Jana-Marie/Enlightened-Otter/HW/V2.1/front.jpg

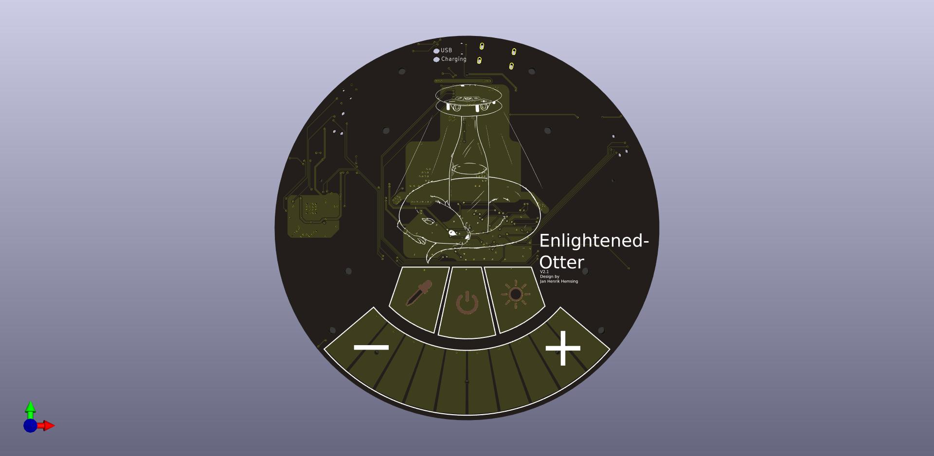
HW/V2.1/front.jpg
