Jana-Marie/Enlightened-Otter/Images/4cb7e35a-7c68-4c7e-90ba-2f1905d7ad42.jpeg

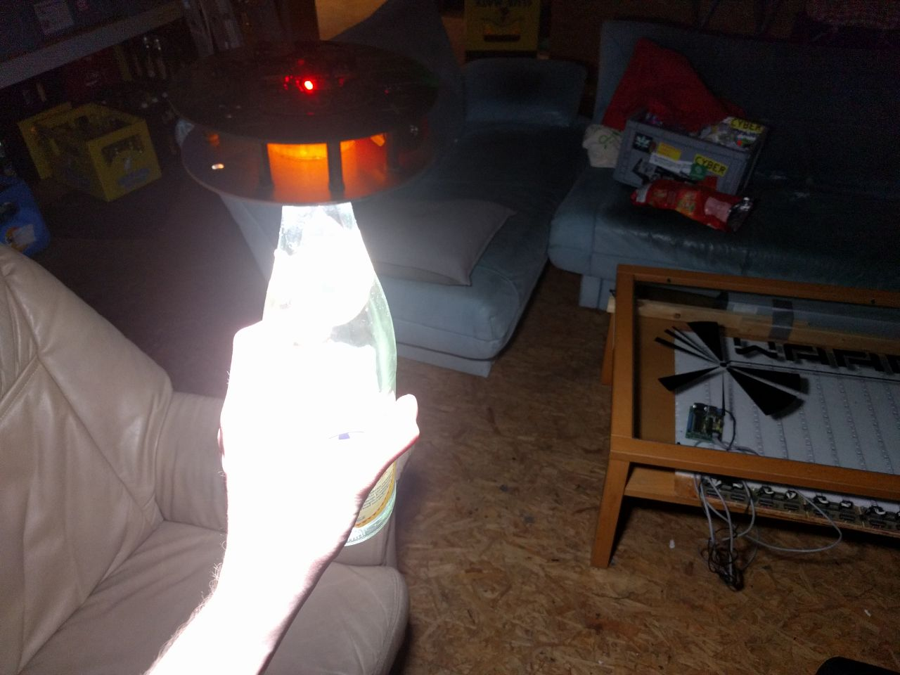
Images/4cb7e35a-7c68-4c7e-90ba-2f1905d7ad42.jpeg
