Jana-Marie/Enlightened-Otter/Images/final_kueche.jpeg

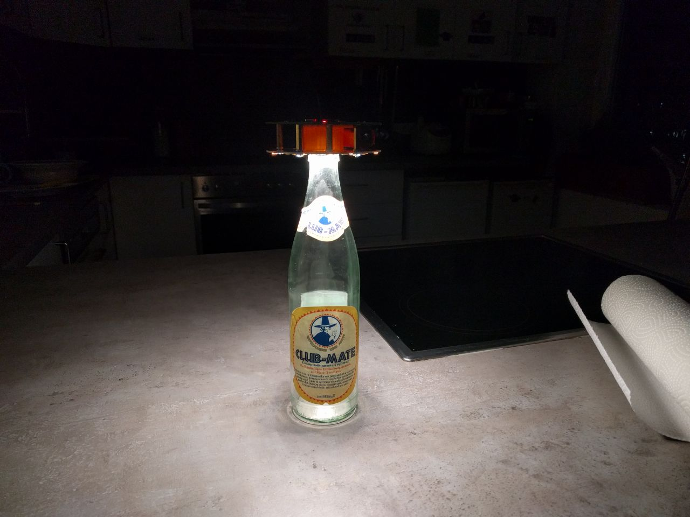
Images/final_kueche.jpeg
