Jana-Marie/Enlightened-Otter/Images/front_1.jpeg

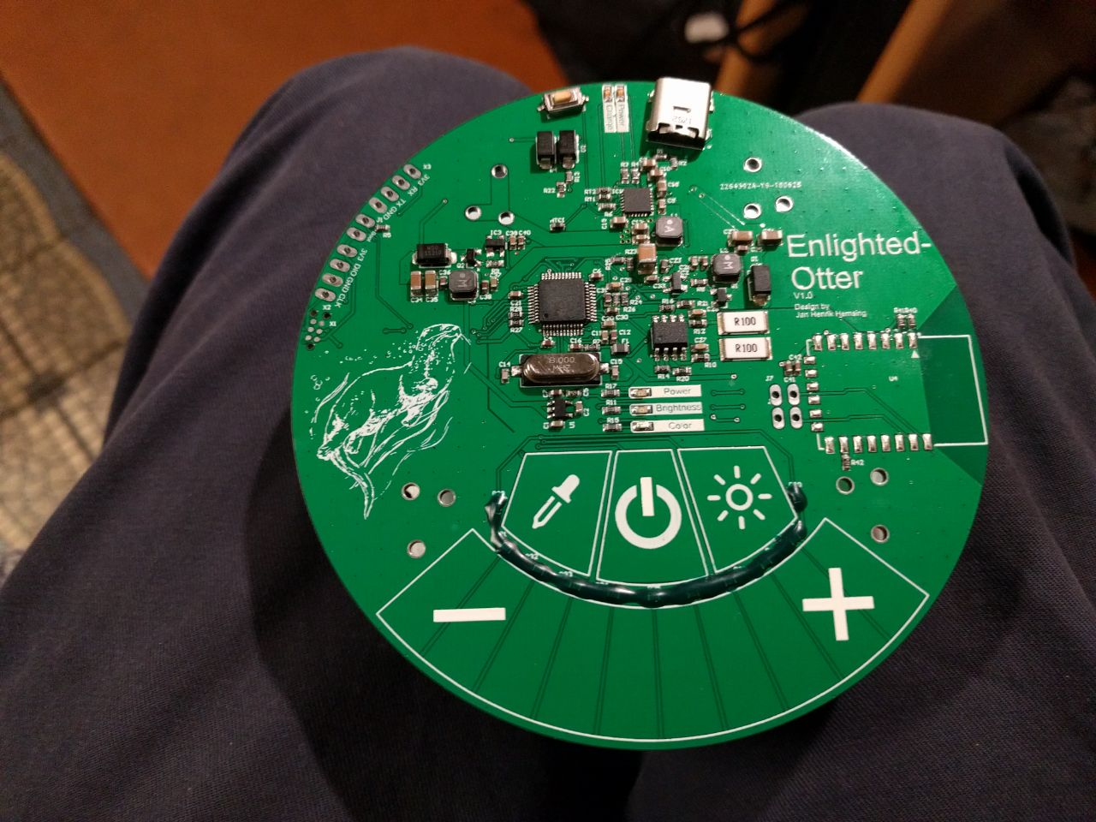
Images/front_1.jpeg
