Jana-Marie/Enlightened-Otter/Images/front_usb_1.jpeg

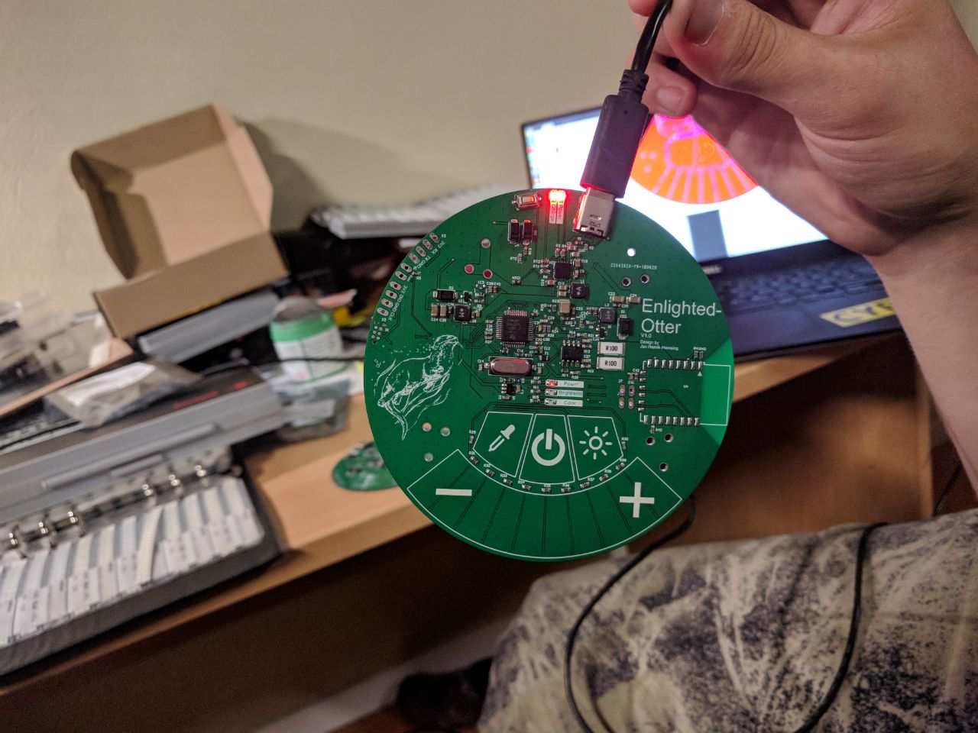
Images/front_usb_1.jpeg
