Jana-Marie/Enlightened-Otter/Images/light_1.jpeg

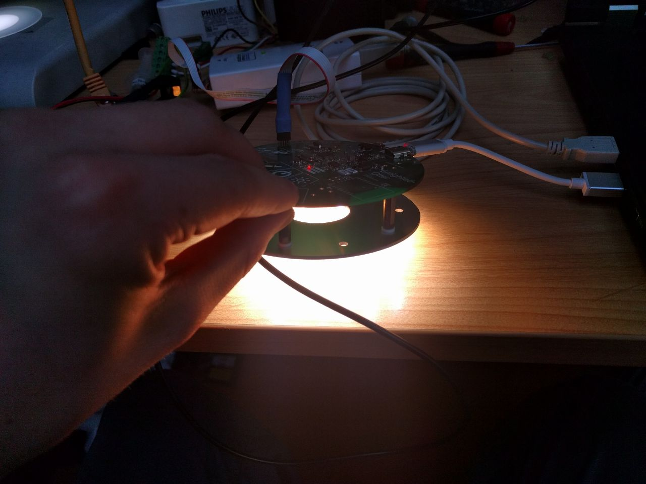
Images/light_1.jpeg
