Jana-Marie/Enlightened-Otter/Images/programming_1.jpeg

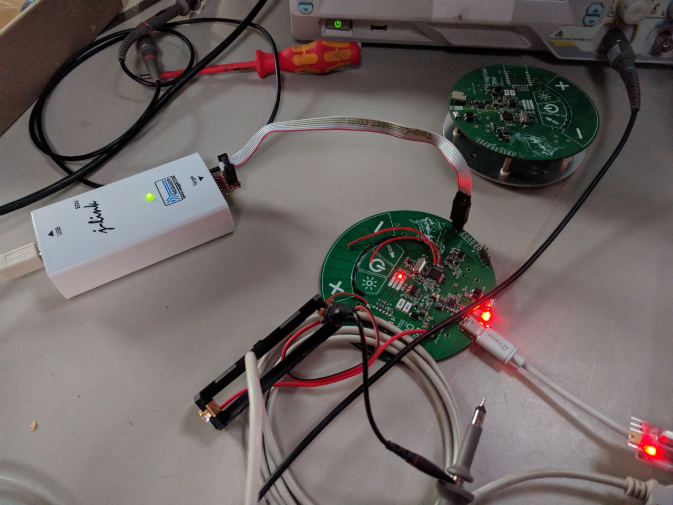
Images/programming_1.jpeg
