Jana-Marie/Enlightened-Otter/Images/spacer_3.jpeg

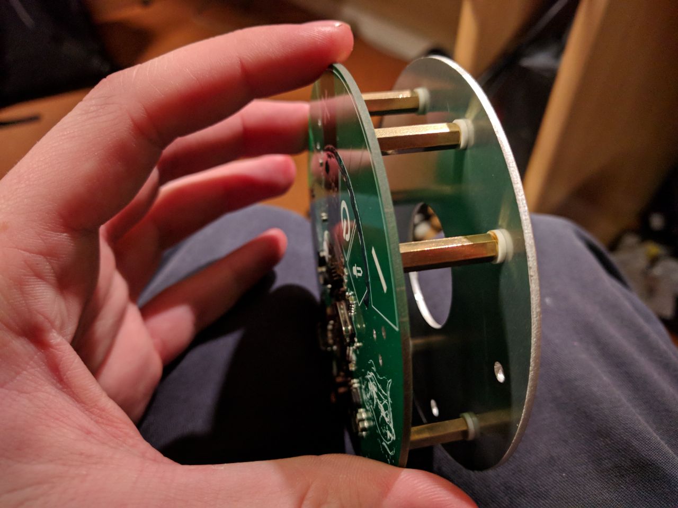
Images/spacer_3.jpeg
