Jana-Marie/Enlightened-Otter/Images/v21_1.jpg

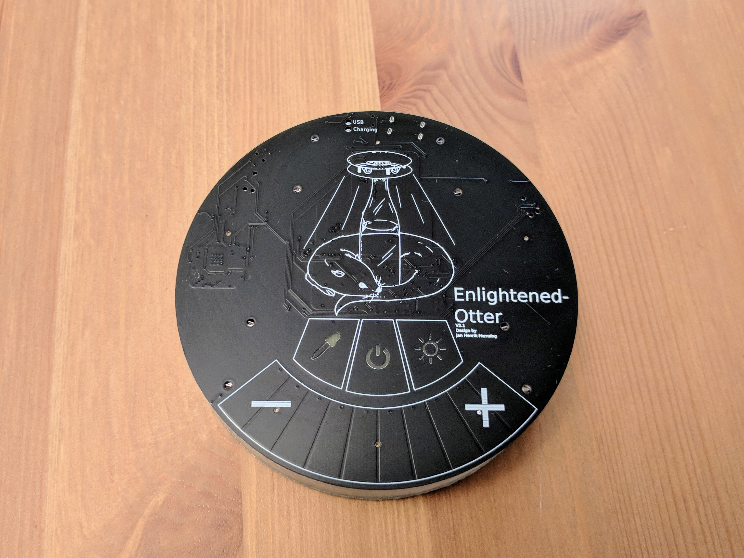
Images/v21_1.jpg
