Jana-Marie/Enlightened-Otter/Images/v21_back_2.jpg

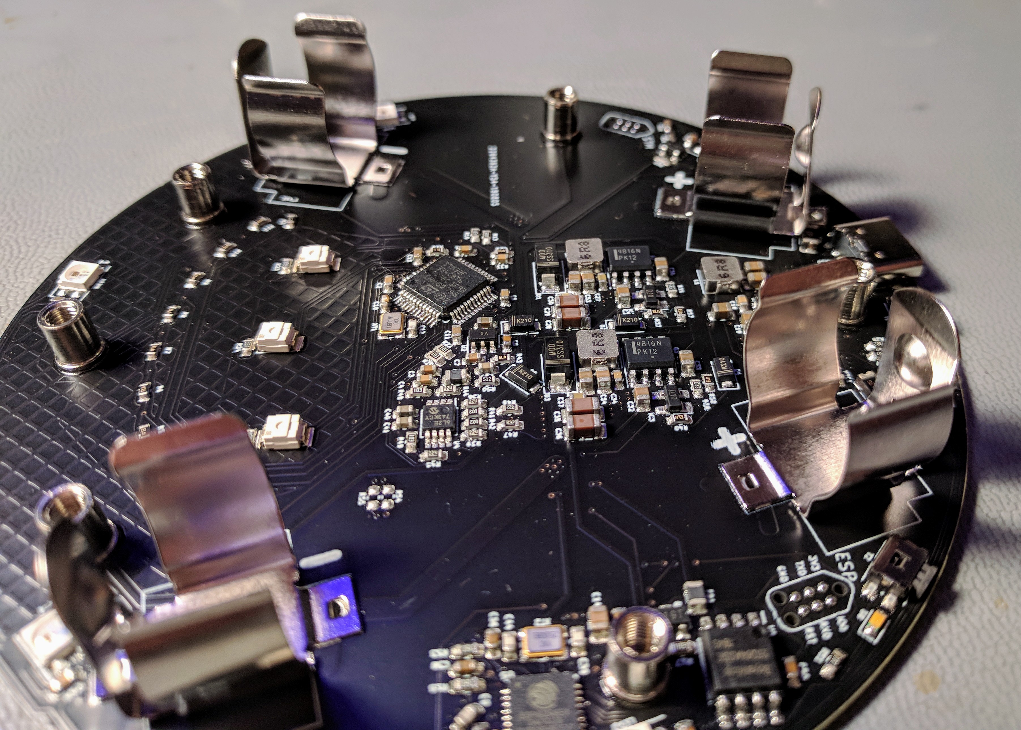
Images/v21_back_2.jpg
