Jana-Marie/Enlightened-Otter/Images/v21_mate_1.jpg

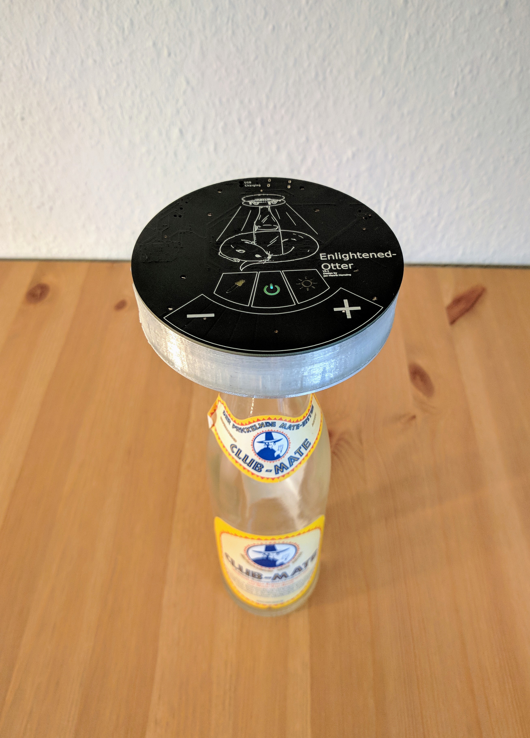
Images/v21_mate_1.jpg
