Jana-Marie/Enlightened-Otter/Images/v21_moodlight_2.jpg

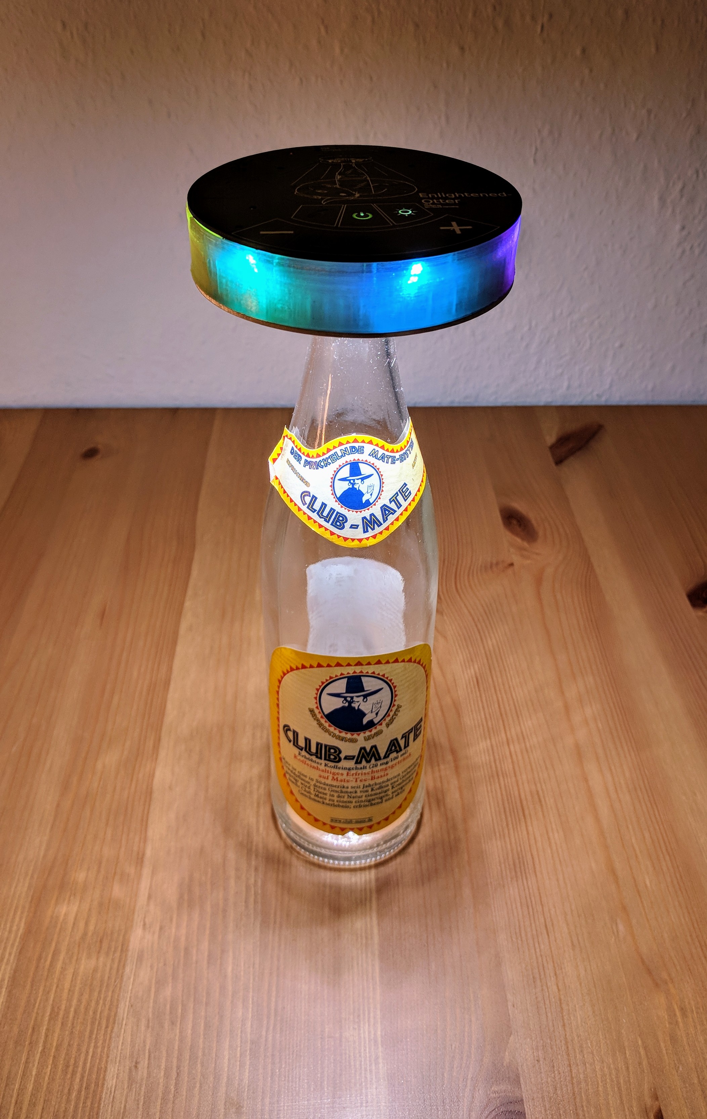
Images/v21_moodlight_2.jpg
