Jana-Marie/Enlightened-Otter/Images/v21_moodlight_3.jpg

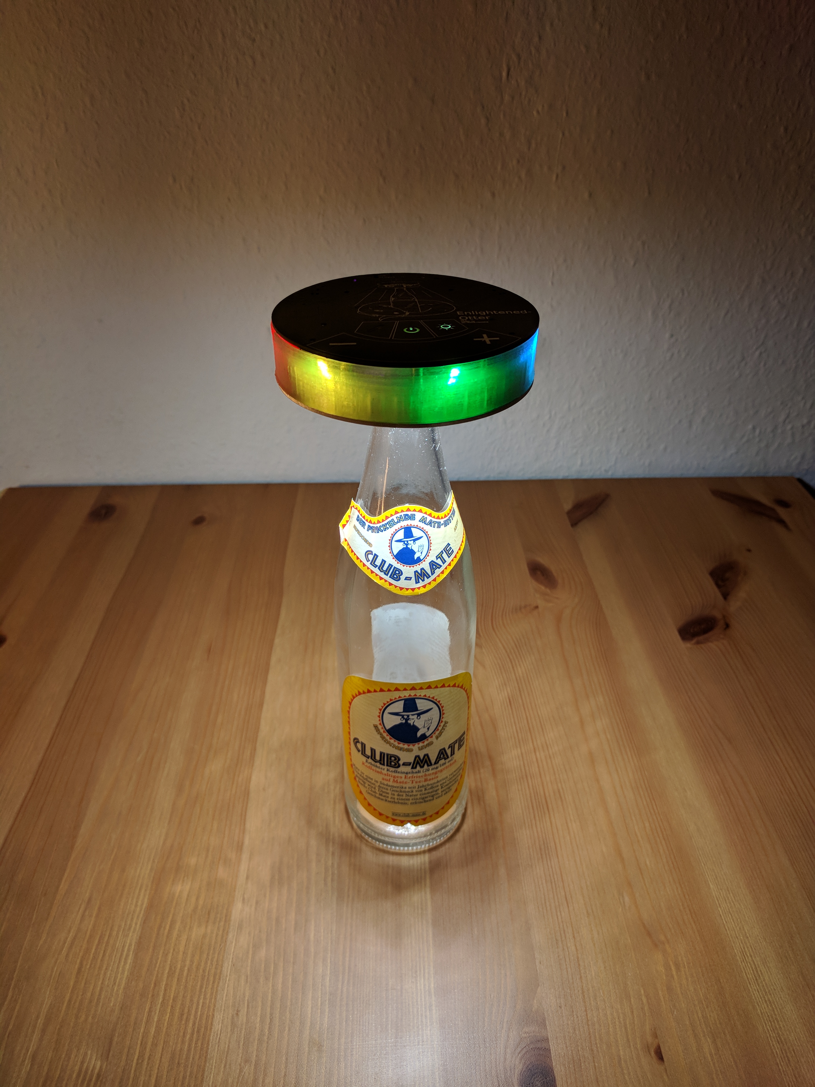
Images/v21_moodlight_3.jpg
