Jana-Marie/Enlightened-Otter/Images/v21_on_1.jpg

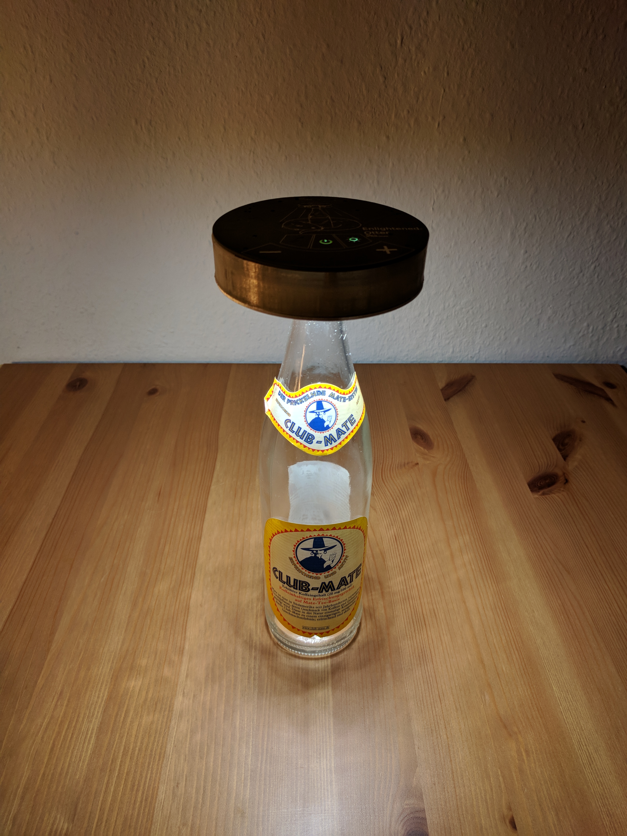
Images/v21_on_1.jpg
