Jana-Marie/Enlightened-Otter/HW/Sim/Boost.asc

C1: cap; 4.7µ; V=25 Irms=0 Rser=0.003 Lser=0
C2: cap; 10µ; V=25 Irms=0 Rser=0.001 Lser=0 mfg="TDK" pn="C575OX7RIE106M" type="X7R"
C3: cap; 4.7µ; V=25 Irms=0 Rser=0.003 Lser=0
D1: schottky; SS24
L1: ind; {hen}; Ipk=3.7 Rser=0.042 Rpar=15188 Cpar=3.369p
M1: nmos; FDS5690
R1: res; {res}; tol=1 pwr=1
R2: res; 5; tol=1 pwr=1
V1: voltage; 4.2; Rser=0
V2: voltage; PULSE(0 5 0 0 0 {0.715/freq} {1/freq}); Rser=5
Named nets: 0, VOUT, VIN, GATE
.tran 0 0.001 0.00095
.step param hen 1µ 15µ 200n
.meas Pin RMS -V(vin)*I(V1)
.meas Pout RMS V(vout)*I(R1)
.meas Eff PARAM Pout/Pin*100.0
.param res=85 freq=750k
