Jana-Marie/Enlightened-Otter/Inc/gamma.h

/*
 * Enlightened-Otter  -  Stm32f334 based mobile worklight.
 * Copyright (C) 2019 Jan Henrik Hemsing
 *
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
 * You should have received a copy of the GNU General Public License along with
 * this program.  If not, see <http://www.gnu.org/licenses/>.
 */
 #pragma once

float gammaTable[] = { // generated gamma correction table from Tools/gamma.py gamma value used: 1.6 resolution: 1.00000
	0.50,	0.52,	0.57,	0.64,	0.72,	0.82,	0.92,	1.04,	1.17,	1.31,	1.46,	1.61,	1.78,	1.96,	2.14,	2.33,
	2.53,	2.74,	2.95,	3.17,	3.40,	3.63,	3.88,	4.13,	4.38,	4.64,	4.91,	5.19,	5.47,	5.75,	6.05,	6.35,
	6.65,	6.96,	7.28,	7.60,	7.93,	8.26,	8.60,	8.94,	9.29,	9.64,	10.00,	10.37,	10.74,	11.11,	11.49,	11.88,
	12.27,	12.66,	13.06,	13.46,	13.87,	14.29,	14.71,	15.13,	15.56,	15.99,	16.43,	16.87,	17.31,	17.76,	18.22,	18.68,
	19.14,	19.61,	20.08,	20.56,	21.04,	21.53,	22.02,	22.51,	23.01,	23.51,	24.02,	24.53,	25.04,	25.56,	26.08,	26.61,
	27.14,	27.68,	28.22,	28.76,	29.30,	29.86,	30.41,	30.97,	31.53,	32.10,	32.67,	33.24,	33.82,	34.40,	34.98,	35.57,
	36.17,	36.76,	37.36,	37.97,	38.57,	39.18,	39.80,	40.42,	41.04,	41.66,	42.29,	42.93,	43.56,	44.20,	44.85,	45.49,
	46.14,	46.80,	47.45,	48.11,	48.78,	49.45,	50.12,	50.79,	51.47,	52.15,	52.84,	53.52,	54.21,	54.91,	55.61,	56.31,
	57.01,	57.72,	58.43,	59.15,	59.87,	60.59,	61.31,	62.04,	62.77,	63.50,	64.24,	64.98,	65.73,	66.47,	67.22,	67.98,
	68.73,	69.49,	70.26,	71.02,	71.79,	72.56,	73.34,	74.12,	74.90,	75.68,	76.47,	77.26,	78.06,	78.85,	79.65,	80.46,
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
	444.16,	445.69,	447.22,	448.75,	450.29,	451.83,	453.37,	454.91,	456.46,	458.00,	459.55,	461.10,	462.66,	464.21,	465.77,	467.33,
	468.89,	470.45,	472.01,	473.58,	475.15,	476.72,	478.29,	479.86,	481.44,	483.02,	484.60,	486.18,	487.76,	489.35,	490.93,	492.52,
	494.12,	495.71,	497.30,	498.90 };
