Jana-Marie/Enlightened-Otter/Src/utils.c

/*
 * Enlightened-Otter  -  Stm32f334 based mobile worklight.
 * Copyright (C) 2019 Jan Henrik Hemsing
 *
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
 * You should have received a copy of the GNU General Public License along with
 * this program.  If not, see <http://www.gnu.org/licenses/>.
 */

#include "utils.h"
#include "ntc.h"
#include "gamma.h"
#include "variables.h"

extern struct status_t stat;

void RT_adc_task(void){
	if (read_RT_status(ADC_DONE_MASK) == 0) {
		switch (stat.state)
		{
		case 0:
			stat.vIn = read_RT_ADC();//* 0.01f;
			configure_RT(CHG_ADC, ADC_IBUS);
			stat.state = 1;
			break;
		case 1:
			stat.iIn = read_RT_ADC();// * 0.05f;
			configure_RT(CHG_ADC, ADC_VBAT);
			stat.state = 2;
			break;
		case 2:
			stat.vBatRt = read_RT_ADC();// * 0.005f;
			configure_RT(CHG_ADC, ADC_IBAT);
			stat.state = 3;
			break;
		case 3:
			stat.iBat = read_RT_ADC();// * 0.05f;
			configure_RT(CHG_ADC, ADC_NTC);
			stat.state = 4;
			break;
		case 4:
			stat.batTemp = read_RT_ADC();
			configure_RT(CHG_ADC, ADC_VBUS2);
			stat.state = 0;
			break;
		default:
			break;
		}
		stat.errCnt = 0;
	} else stat.errCnt++;

	stat.pIn = stat.vIn * stat.iIn / 1000.0f;
	stat.pBat = stat.vBatRt * stat.iBat / 1000.0f;
	stat.pSum = stat.pIn - stat.pBat;
}

void powerdown(void){
	 configure_RT(CHG_CTRL2, TURNOFF_MASK);
}

void enable_OTG(void) {
	configure_RT(CHG_CTRL16, DISABLE_UUG);
	configure_RT(CHG_CTRL1, ENABLE_OTG_MASK);
}

void disable_OTG(void) {
	configure_RT(CHG_CTRL16, ENABLE_UUG);
	configure_RT(CHG_CTRL1, DISABLE_OTG_MASK);
}

float read_RT_ADC(void) {
	uint16_t _cnt = 0;
	uint8_t _ADC_H, _ADC_L;
	uint8_t _tmp_data_H = ADC_DATA_H;
	uint8_t _tmp_data_L = ADC_DATA_L;

	while (HAL_I2C_GetState(&hi2c1) != HAL_I2C_STATE_READY) if (_cnt++ > 10000) break;
	HAL_I2C_Master_Transmit_DMA(&hi2c1, RT_ADDRESS, &_tmp_data_H, 1);
	_cnt = 0;
	while (HAL_I2C_GetState(&hi2c1) != HAL_I2C_STATE_READY) if (_cnt++ > 10000) break;
	HAL_I2C_Master_Receive_DMA(&hi2c1, RT_ADDRESS, &_ADC_H, 1);
	_cnt = 0;
	while (HAL_I2C_GetState(&hi2c1) != HAL_I2C_STATE_READY) if (_cnt++ > 10000) break;
	HAL_I2C_Master_Transmit_DMA(&hi2c1, RT_ADDRESS, &_tmp_data_L, 1);
	_cnt = 0;
	while (HAL_I2C_GetState(&hi2c1) != HAL_I2C_STATE_READY) if (_cnt++ > 10000) break;
	HAL_I2C_Master_Receive_DMA(&hi2c1, RT_ADDRESS, &_ADC_L, 1);
	_cnt = 0;
	while (HAL_I2C_GetState(&hi2c1) != HAL_I2C_STATE_READY) if (_cnt++ > 10000) break;

	float _tmp_data = ((_ADC_H *256) + _ADC_L);
	return _tmp_data;
}

uint8_t read_RT_status(uint8_t _mask){
	uint8_t ret;
	uint8_t _cnt = 0;
	uint8_t _register = CHG_STAT;

	while (HAL_I2C_GetState(&hi2c1) != HAL_I2C_STATE_READY) if (_cnt++ > 10000) break;
	HAL_I2C_Master_Transmit_DMA(&hi2c1, RT_ADDRESS, &_register, 1);
	_cnt = 0;
    while (HAL_I2C_GetState(&hi2c1) != HAL_I2C_STATE_READY) if (_cnt++ > 10000) break;
	HAL_I2C_Master_Receive_DMA(&hi2c1, RT_ADDRESS, &ret, 1);
	_cnt = 0;
	while (HAL_I2C_GetState(&hi2c1) != HAL_I2C_STATE_READY) if (_cnt++ > 10000) break;
	ret = ret & _mask;
	return ret;
}

uint8_t read_RT_register(uint8_t _register){
	uint8_t ret;
	uint8_t _cnt = 0;

	while (HAL_I2C_GetState(&hi2c1) != HAL_I2C_STATE_READY) if (_cnt++ > 10000) break;
	HAL_I2C_Master_Transmit_DMA(&hi2c1, RT_ADDRESS, &_register, 1);
	_cnt = 0;
    while (HAL_I2C_GetState(&hi2c1) != HAL_I2C_STATE_READY) if (_cnt++ > 10000) break;
	HAL_I2C_Master_Receive_DMA(&hi2c1, RT_ADDRESS, &ret, 1);
	_cnt = 0;
	while (HAL_I2C_GetState(&hi2c1) != HAL_I2C_STATE_READY) if (_cnt++ > 10000) break;
	return ret;
}


void RT_Init(void) {
  // Configure the RT9466, set currents to maximum
  configure_RT(CHG_CTRL2, IINLIM_MASK);
  configure_RT(CHG_CTRL3, SET_ILIM_3A);
	configure_RT(CHG_CTRL1,ENABLE_STAT_LED_MASK);
  configure_RT(CHG_ADC, ADC_VBUS2);
}

void configure_RT(uint8_t _register, uint8_t _mask) {
  uint16_t _cnt = 0;
  uint8_t _tmp_data[2] = {_register, _mask};
  while (HAL_I2C_GetState(&hi2c1) != HAL_I2C_STATE_READY) if (_cnt++ > 10000) break;
  HAL_I2C_Master_Transmit_DMA(&hi2c1, RT_ADDRESS, _tmp_data, 2);
  _cnt = 0;
  while (HAL_I2C_GetState(&hi2c1) != HAL_I2C_STATE_READY) if (_cnt++ > 10000) break;
}


void set_pwm(uint8_t timer, float duty) {

	/* Clamp duty cycle values */
	if (duty < MIN_DUTY) duty = MIN_DUTY;
	if (duty > MAX_DUTY) duty = MAX_DUTY;
	uint16_t _per = HRTIM_PERIOD * duty;
	/* Set registers according to duty cycle */
	HRTIM1->sTimerxRegs[timer].CMP1xR = _per;
		//HRTIM1->sTimerxRegs[timer].CMP2xR = (_per % 32);
		//HRTIM1->sTimerxRegs[timer].SETx1R = HRTIM_SET1R_CMP2;
	//	HRTIM1->sTimerxRegs[timer].RSTx1R = HRTIM_RST1R_CMP1;
		//HRTIM1->sTimerxRegs[timer].PERxR  = HRTIM_PERIOD;
		//HRTIM1->sTimerxRegs[HRTIM_TIMERID_MASTER].PERxR = HRTIM_PERIOD + 2;
}

float ntc_calc(uint16_t adc_value) {

	int16_t p1, p2;
	p1 = NTC_table[(adc_value >> 7)];
	p2 = NTC_table[(adc_value >> 7) + 1];

	return (p1 - ( (p1 - p2) * (adc_value & 0x007F) ) / 128.0f ) / 2.0f;
}

float gamma_calc(float target){
	float p1,p2;

	p1 = gammaTable[(int)target];
	p2 = gammaTable[(int)target+1];

	return (p1 + ((p1-p2)*((int)target-target)));
}

#if defined(SCOPE_CHANNELS)
void set_scope_channel(uint8_t ch, int16_t val) {
	ch_buf[ch] = val;
}

void console_scope(void) {
	memset(uart_buf, 0, sizeof(uart_buf));

#if (SCOPE_CHANNELS == 1)
	sprintf((char*)uart_buf, "%i\n\r", ch_buf[0]);
#elif (SCOPE_CHANNELS == 2)
	sprintf((char*)uart_buf, "%i\t%i\n\r", ch_buf[0], ch_buf[1]);
#elif (SCOPE_CHANNELS == 3)
	sprintf((char*)uart_buf, "%i\t%i\t%i\n\r", ch_buf[0], ch_buf[1], ch_buf[2]);
#elif (SCOPE_CHANNELS == 4)
	sprintf((char*)uart_buf, "%i\t%i\t%i\t%i\n\r", ch_buf[0], ch_buf[1], ch_buf[2], ch_buf[3]);
#elif (SCOPE_CHANNELS == 5)
	sprintf((char*)uart_buf, "%i\t%i\t%i\t%i\t%i\n\r", ch_buf[0], ch_buf[1], ch_buf[2], ch_buf[3], ch_buf[4]);
#elif (SCOPE_CHANNELS == 6)
	sprintf((char*)uart_buf, "%i\t%i\t%i\t%i\t%i\t%i\n\r", ch_buf[0], ch_buf[1], ch_buf[2], ch_buf[3], ch_buf[4], ch_buf[5]);
#elif (SCOPE_CHANNELS == 7)
	sprintf((char*)uart_buf, "%i\t%i\t%i\t%i\t%i\t%i\t%i\n\r", ch_buf[0], ch_buf[1], ch_buf[2], ch_buf[3], ch_buf[4], ch_buf[5], ch_buf[6]);
#elif (SCOPE_CHANNELS == 8)
	sprintf((char*)uart_buf, "%i\t%i\t%i\t%i\t%i\t%i\t%i\t%i\n\r", ch_buf[0], ch_buf[1], ch_buf[2], ch_buf[3], ch_buf[4], ch_buf[5], ch_buf[6], ch_buf[7]);
#endif

	HAL_UART_Transmit_DMA(&huart1, (uint8_t *)uart_buf, strlen((char*)uart_buf));
	huart1.gState = HAL_UART_STATE_READY;
}
#endif
